heuristic-industries/switch-mod/firmware/src/toggle_switch.rs

use crate::SwitchTimer;
use attiny_hal::{clock, delay};
use core::fmt::Debug;
use embedded_hal::{
    digital::v2::{InputPin, OutputPin},
    prelude::_embedded_hal_blocking_delay_DelayMs,
};

pub struct ToggleSwitch<Input, Output> {
    input: Input,
    output: Output,
    default_state: bool,
    pub active: bool,
    previous_state: bool,
    delay: delay::Delay<clock::MHz1>,
}

impl<Input, Output> ToggleSwitch<Input, Output>
where
    Input: InputPin,
    Output: OutputPin,
    Input::Error: Debug,
    Output::Error: Debug,
{
    pub fn new(input: Input, output: Output, default_state: bool, active: bool) -> Self {
        let delay = delay::Delay::<clock::MHz1>::new();

        ToggleSwitch {
            input,
            output,
            default_state,
            active,
            previous_state: false,
            delay,
        }
    }

    pub fn init(&mut self) {
        // occasionally the bypass circuit we're interfacing with
        // will take longer to charge/boot than we do, so wait a sec
        // 500ms seems reasonable enough, right?
        self.delay.delay_ms(250 as u8);
        self.delay.delay_ms(250 as u8);
        self.delay.delay_ms(250 as u8);
        self.delay.delay_ms(250 as u8);
        self.delay.delay_ms(250 as u8);
        self.delay.delay_ms(250 as u8);
        self.delay.delay_ms(250 as u8);
        self.delay.delay_ms(250 as u8);
        self.delay.delay_ms(250 as u8);
        self.delay.delay_ms(250 as u8);

        if self.active ^ self.default_state {
            self.pulse();
        }
    }

    pub fn on_change(&mut self, timer: &mut SwitchTimer) -> bool {
        let pressed = self.is_pressed();

        if pressed == self.previous_state || !timer.debounce.threshold_reached {
            return false;
        }

        timer.debounce.reset();

        self.previous_state = pressed;

        if pressed {
            timer.hold.reset();

            self.set_state(!self.active);
        } else if timer.hold.threshold_reached {
            self.set_state(false);
        }

        true
    }

    fn is_pressed(&mut self) -> bool {
        self.input.is_low().unwrap()
    }

    fn set_state(&mut self, state: bool) {
        self.active = state;
        self.pulse();
    }

    fn pulse(&mut self) {
        self.output.set_high().unwrap();
        self.delay.delay_ms(20 as u8);
        self.output.set_low().unwrap();
    }
}
